KrasiniakTW/PogodaAI-weather-station/hardware/circuit_image.png

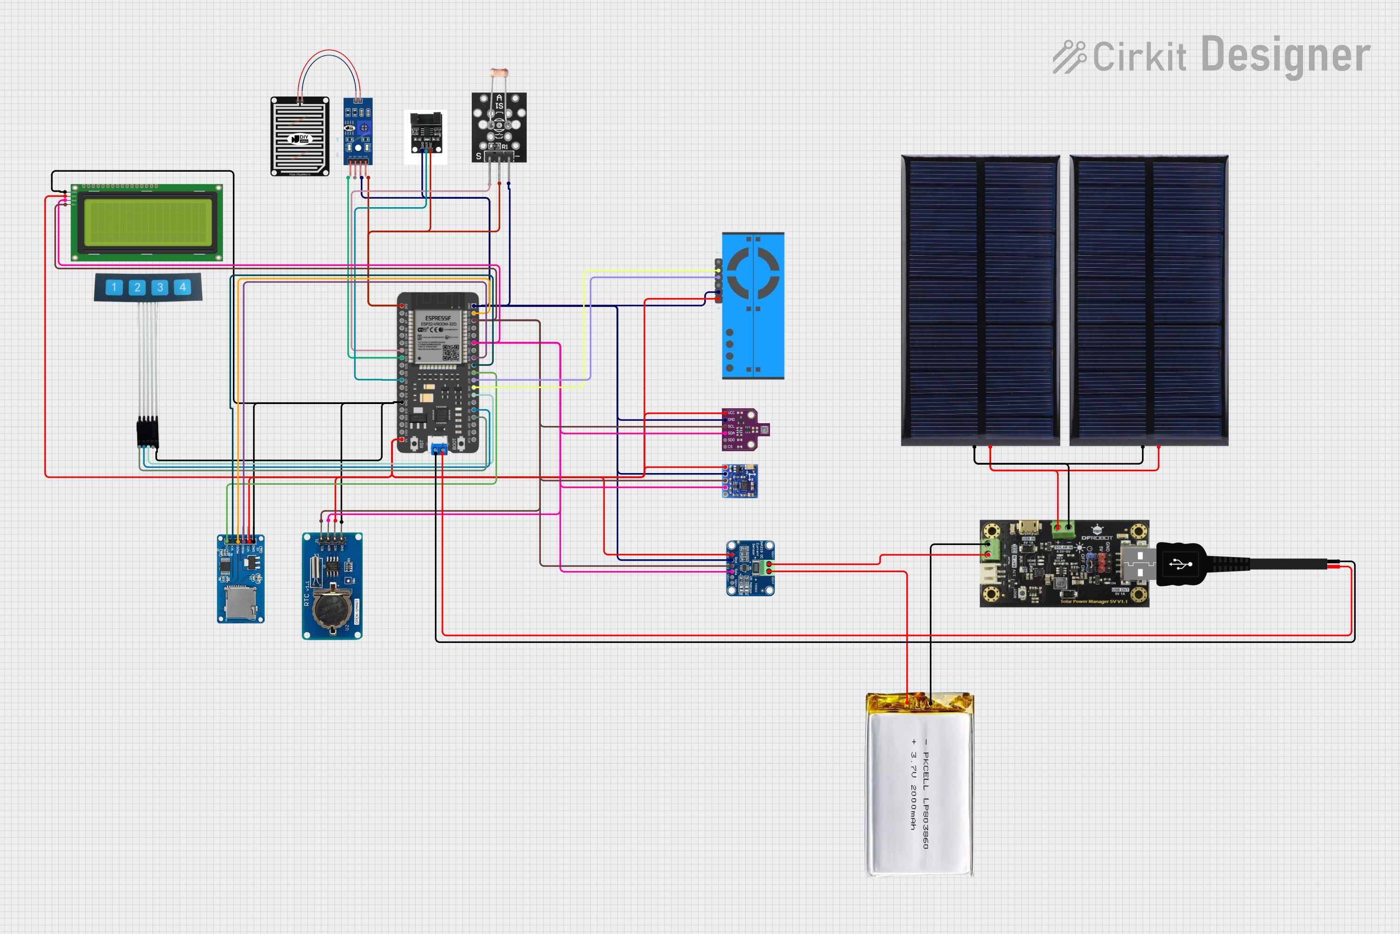
hardware/circuit_image.png
