KrasiniakTW/PogodaAI-weather-station/hardware/photos/screen.JPG

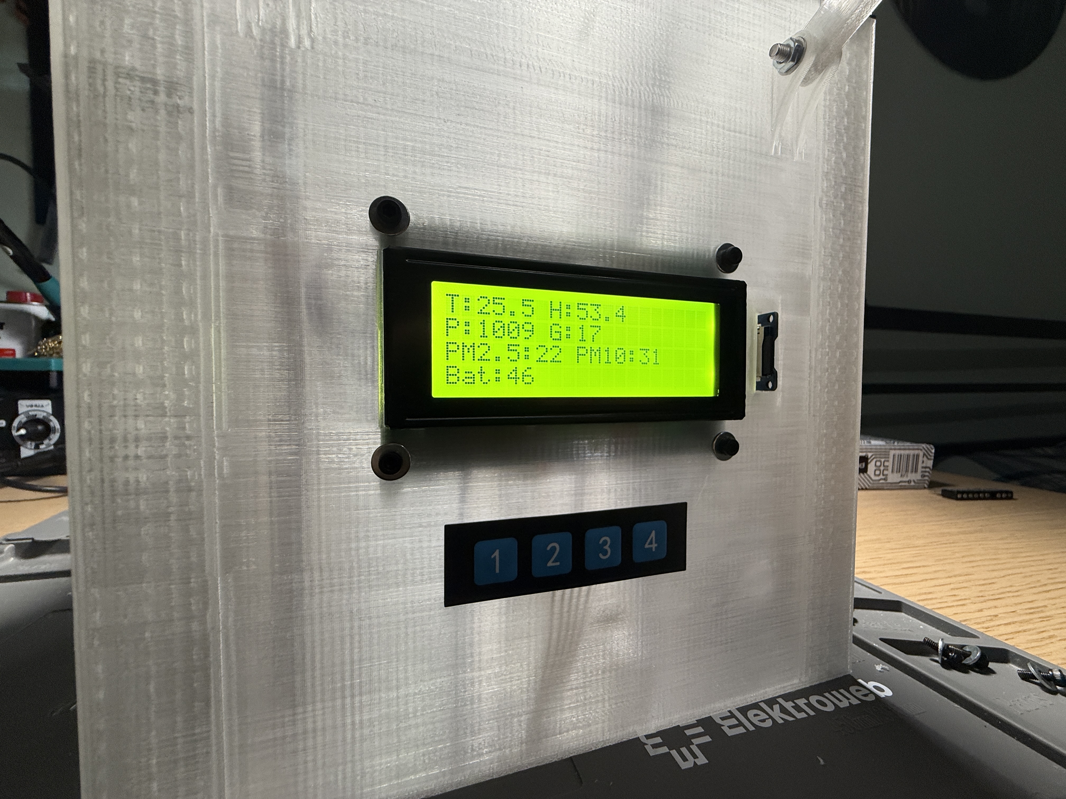
hardware/photos/screen.JPG
