KrasiniakTW/PogodaAI-weather-station/hardware/3d_models/stl/SD_reader_holder.stl

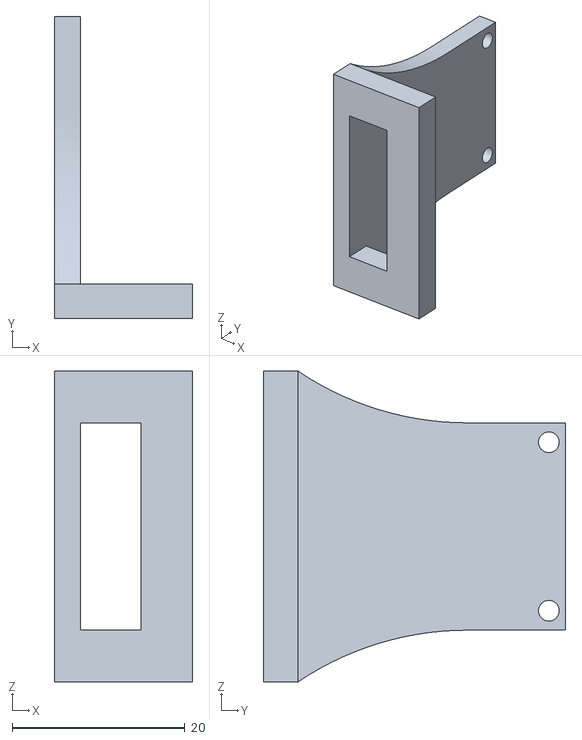
[picture p26: CAD file, 2025-10-12]
hardware/3d_models/stl/SD_reader_holder.stl
16.0 x 35.0 x 36.0
