KrasiniakTW/PogodaAI-weather-station/hardware/3d_models/stl/wind_vane_arrow.stl

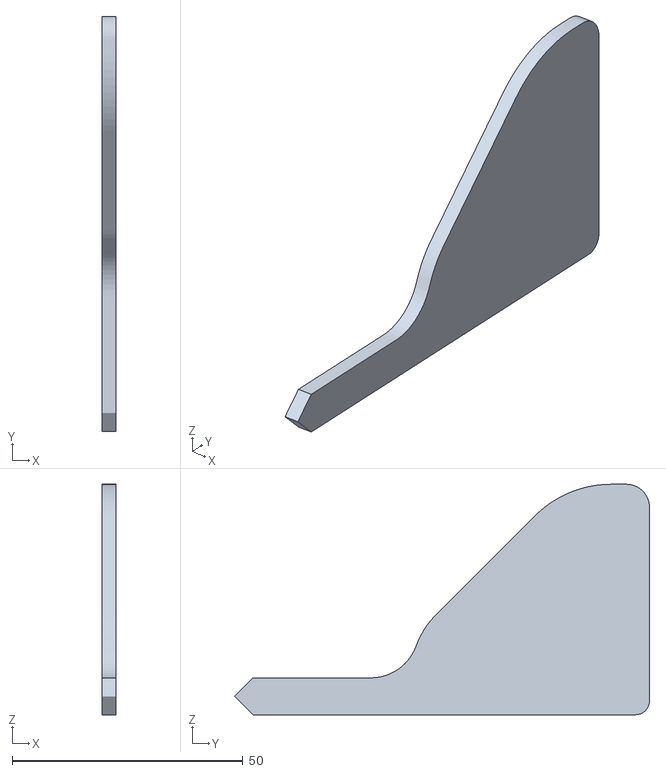
[picture p27: CAD file, 2025-10-12]
hardware/3d_models/stl/wind_vane_arrow.stl
3.00 x 90.0 x 50.0
