KrasiniakTW/PogodaAI-weather-station/hardware/photos/whole_build.png

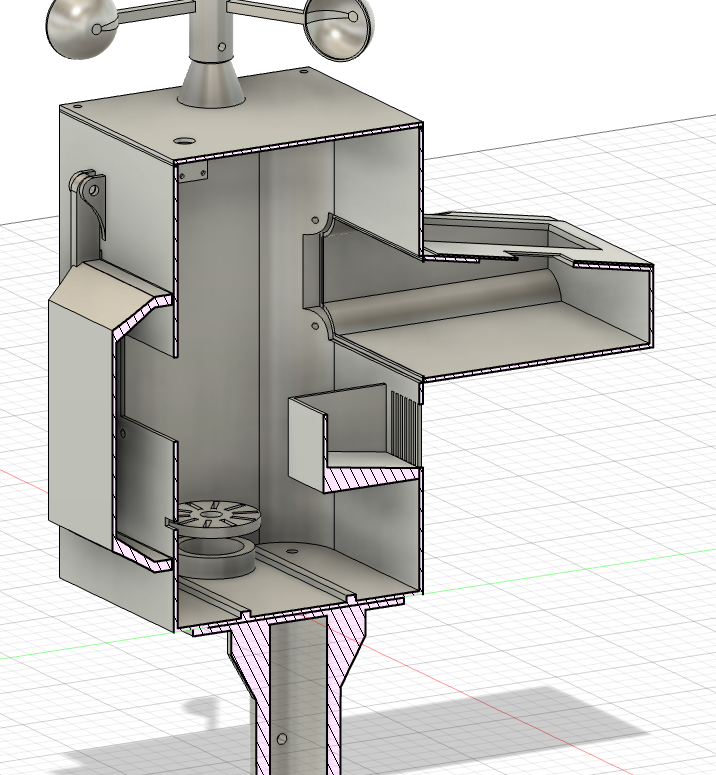
hardware/photos/whole_build.png
